mbovero/808_EQ-Plus_Guitar_Pedal/Images/Digital/Altium_PCB_Top.png

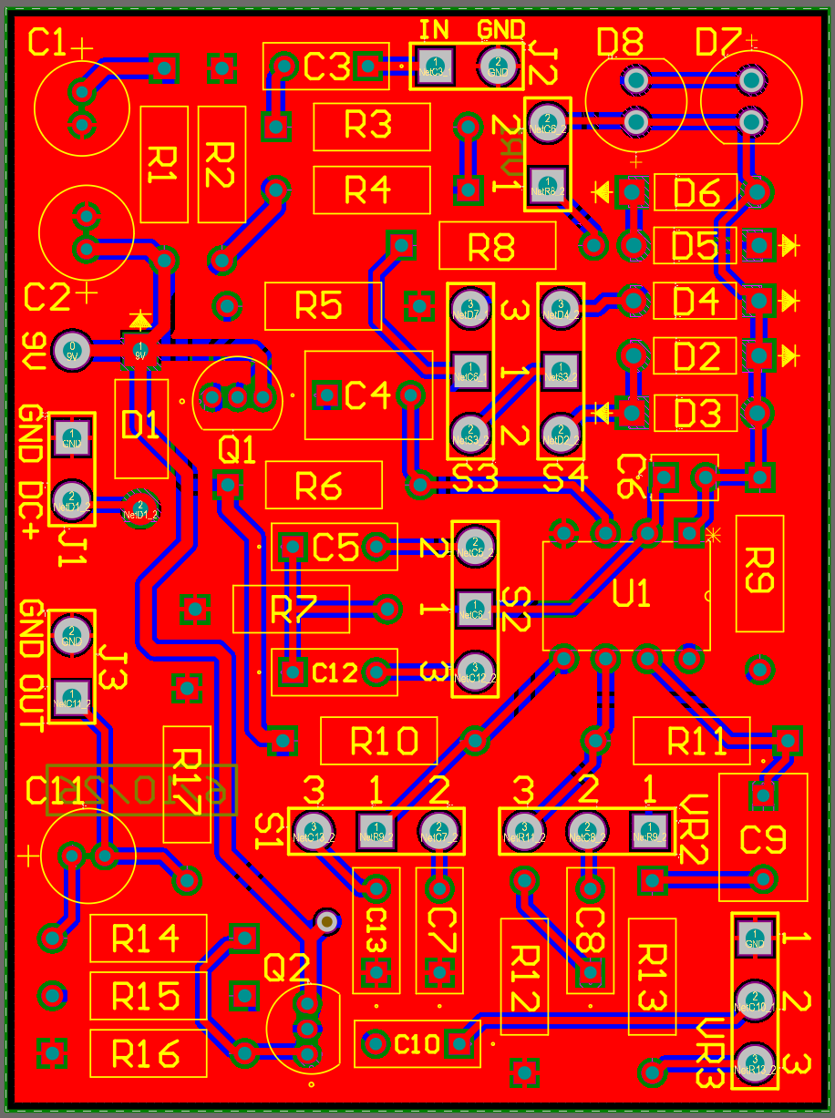
Images/Digital/Altium_PCB_Top.png
