mbovero/808_EQ-Plus_Guitar_Pedal/Images/Digital/BambuStudio_Enclosure_Sliced_Topdown.png

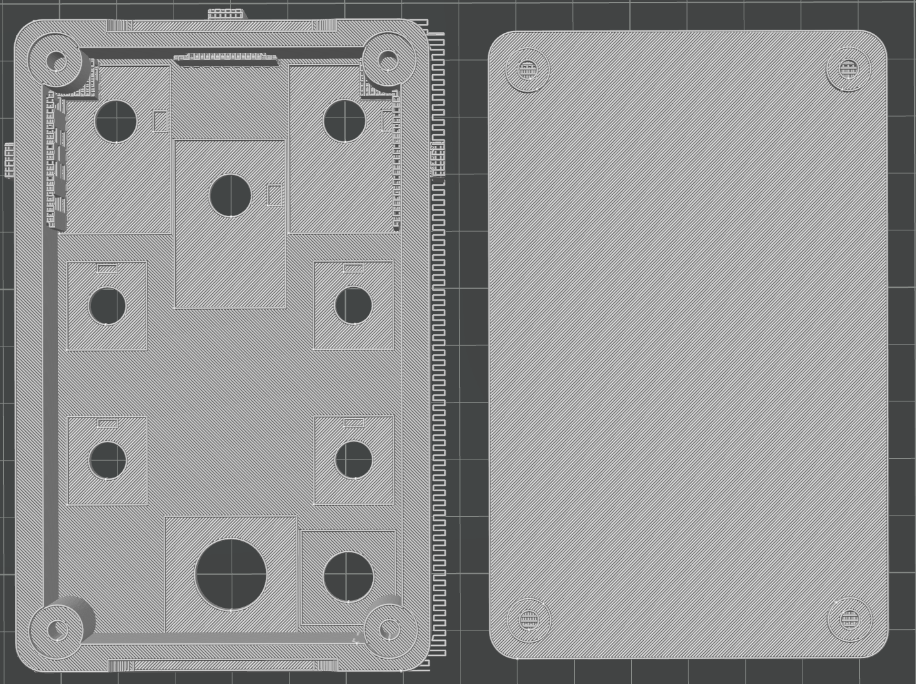
Images/Digital/BambuStudio_Enclosure_Sliced_Topdown.png
