mbovero/808_EQ-Plus_Guitar_Pedal/Images/Digital/Fusion_Bare_Enclosure_Iso_Exploded.png

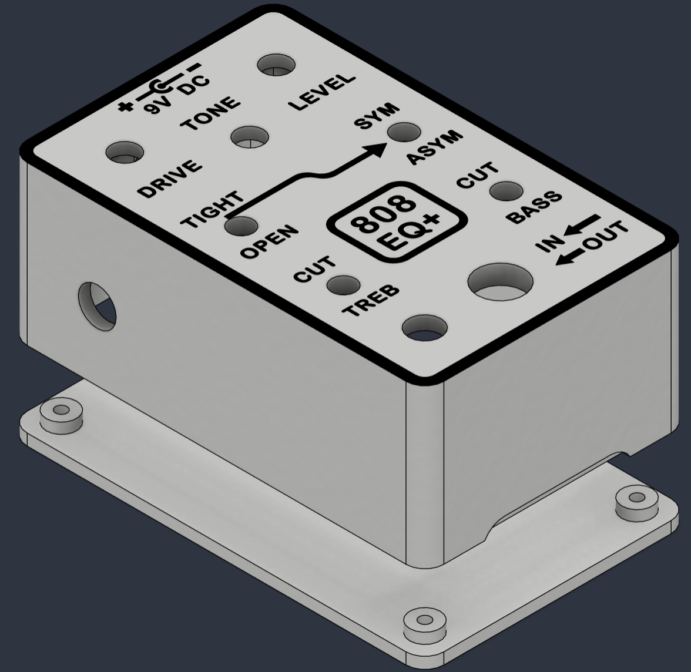
Images/Digital/Fusion_Bare_Enclosure_Iso_Exploded.png
