mbovero/808_EQ-Plus_Guitar_Pedal/Images/Physical/Enclosure_Iso_Bare.jpeg

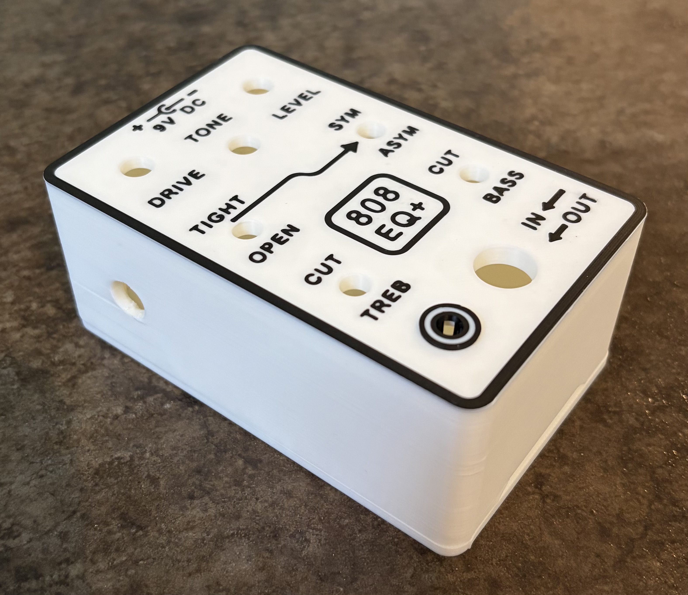
Images/Physical/Enclosure_Iso_Bare.jpeg
