mbovero/808_EQ-Plus_Guitar_Pedal/Images/Physical/Pedal_Inside.jpeg

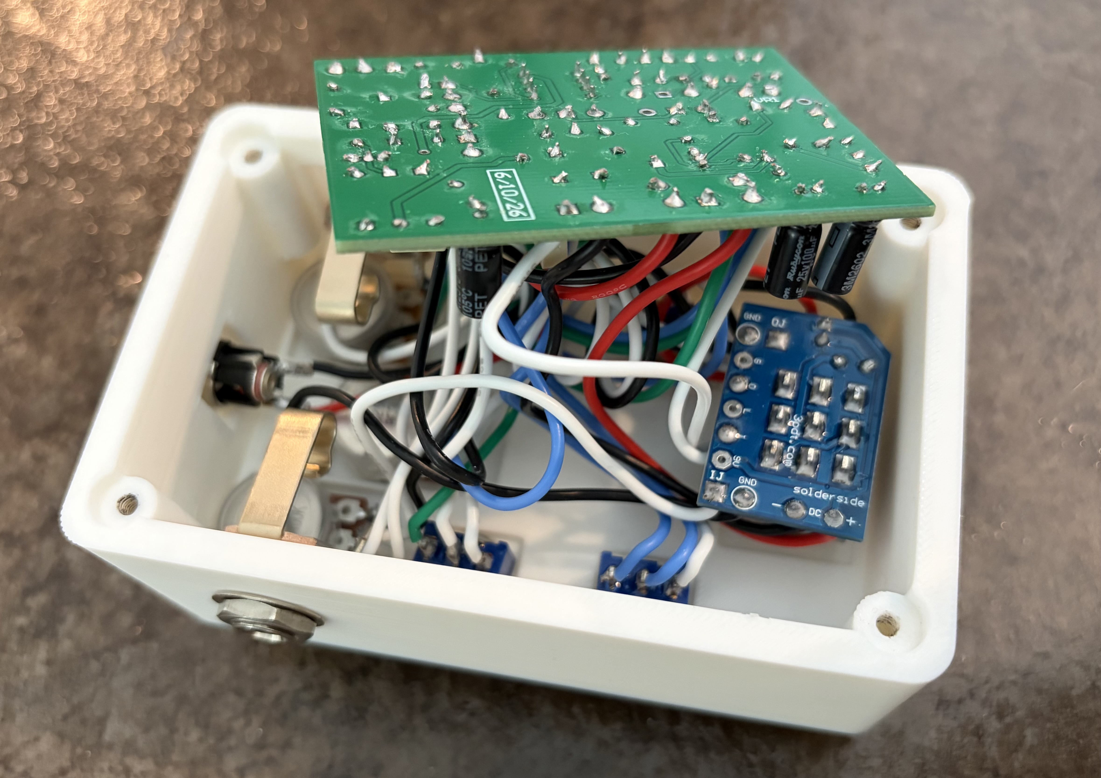
Images/Physical/Pedal_Inside.jpeg
