mbovero/808_EQ-Plus_Guitar_Pedal/Images/Physical/Pedal_Top.jpeg

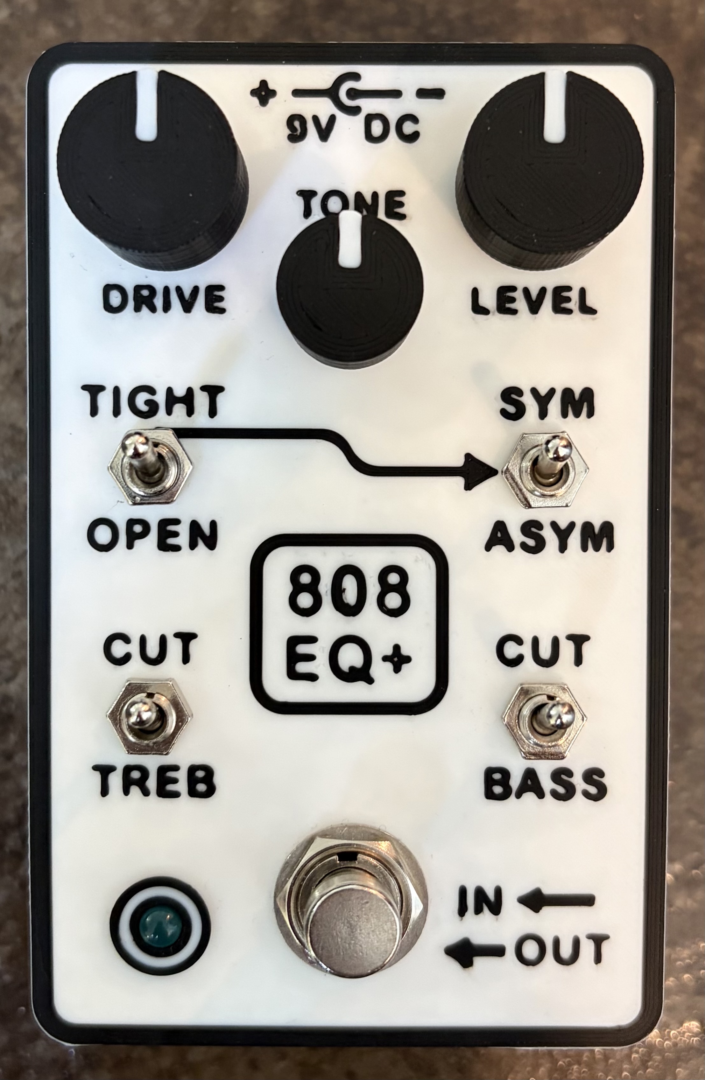
Images/Physical/Pedal_Top.jpeg
