mbovero/808_EQ-Plus_Guitar_Pedal/Design/LTspice/Modded_Tube_Screamer.asc

9VSupply: voltage; SINE(9 0.01 60); AC 0.01
C1: cap; 47µF
C2: cap; 100µF
C3: cap; 0.022µF
C4: cap; 1µF
C5: cap; 0.047µF
C6: cap; 51pF
C7: cap; 0.22µF
C8: cap; 0.22µF
C9: cap; 1µF
C10: cap; 0.1µF
C11: cap; 10µF
C12: cap; 0.082µF
C13: cap; 0.047µF
D1: diode; 1N4007
D2: diode; 1N4148
D3: diode; 1N4148
D4: diode; 1N4148
D5: diode; 1N4148
D6: diode; 1N4148
D7: LED
D8: LED
D9: LED
GuitarIn: voltage; SINE(0 0.2 440); AC 0.2
P1_500K_Log: res; 100k
P2a_20K: res; 10K
P2b_20K: res; 10K
P3a_100K: res; 50K
P3b_100K: res; 50K
Q1: npn; 2N5089
Q2: npn; 2N5089
R1: res; 10K
R2: res; 10K
R3: res; 1K
R4: res; 510K
R5: res; 10K
R6: res; 10K
R7: res; 4.7K
R8: res; 51K
R9: res; 1K
R10: res; 10K
R11: res; 1K
R12: res; 220
R13: res; 1K
R14: res; 100
R15: res; 510K
R16: res; 10K
R17: res; 10K
R18: res; 3.3K
U1_RC4558: UniversalOpAmp2
U2: UniversalOpAmp2
Named nets: 0, 9V, 4V5, BoardOut, GND, BoardIn, Raw9V
.tran 0 3 2.95 10u
.ac dec 1000 20 50000
